misisnik/ExternalInterface/sw/display/window.py

"""
display window
====================
.. moduleauthor:: Michal Sladecek <misisnik@gmail.com>
.. autoclass:: GUI
.. autofunction:: lib

"""
from PIL import Image
from PIL import ImageDraw
from PIL import ImageFont

import os

system_fonts = {'Arial' : 'arial.ttf', 'Big' : 'big.ttf', 'Tiny' : 'tiny.ttf', 'Japan1': 'jpn/7pxkbus.TTF', 'Japan2': 'jpn/enksh__.ttf', 'Japan3': 'jpn/musekinin-katakana.TTF'}
disp_width = 192
disp_height = 64

class GUI(object):
	"""
		There is class for support graphic part of display
	"""
	def __init__(self, rotation = 0):
		"""
			inicialization of gui class
		"""
		#visualisation data - default is blank screen -> every px is off
		self.rotation = rotation #degree of window rotation
		self.reset()
		self.changed = False
		self.display_width = disp_width
		self.display_height = disp_height

	def reset(self):
		"""
			Reset all screen 
		"""
		self.data = [0x00] * 1536
		#create new image object
		if self.rotation == 90:
			self.display_width = disp_height
			self.display_height = disp_width
		else:
			self.display_width = disp_width
			self.display_height = disp_height
		self.image = Image.new('1', (self.display_width, self.display_height))
		self.draw = ImageDraw.Draw(self.image)

	def getBitmap(self, vertical = True):
		"""
			Get finish picture which has to show on display - generating bitmap array
		"""

		d = [""]*1536
		if vertical:
			#for ist3020
			self.finall_image = self.image.rotate(self.rotation)
			dat = self.finall_image.load()
			page = 0
			for i in range(0, self.display_height):
				if i%8 == 0 and i != 0:
					page += 1
				for c in range(0, self.display_width):
					if dat[(c,i)] == 255:
						dat[(c,i)] = 1
					d[(page * self.display_width) + c] += str(dat[(c,i)])
		else:
			#matrix orbital
			dat = self.image.load()
			data = ""
			c = 1
			for r in range(64):
				for l in range(192):
					data += str(dat[(l, r)])
			for i in range(1536):
				d[i] = data[i*8:(i*8)+8]
			#for matrix orbithal
		self.data = [int(i,2) for i in d]

	def addMultilineText(self, text, size = 10, x = 0, y = 0, align = "left", f = 'Arial', spacing = 1, fill = 1):
		"""
			Add multiline text to picture 
				text - data of text
				size - px size of letter
				x	 - x position
				y	 - y position

			return total lines, lines to print, array of text
		"""
		if align not in ['left', 'center', 'right']:
			align = 'left'
		#get width of text
		text_width, text_height = self.getMultilineTextSize(text, size, f)
		lines = 1
		lines_to_print = 1
		new_text = []
		#multiline text - parse to more line
		if text_width > self.display_width or text_height > self.display_height:
			longest = 0
			lines = 0
			new_text = [""]
			for i in text:
				wn, hn = self.getMultilineTextSize(new_text[-1], size, f)
				if wn > self.display_width:
					#check if we're not in the midle of world
					last = new_text[-1]
					for count, l in enumerate(last[::-1]):
						if l == " ":
							break;
					if count > 0 and count < 10:
						del new_text[-1]
						new_text.append(last[0:len(last) - count])
						new_text.append(last[len(last) - count:])
					else:
						new_text.append("")

				if i == "\n":
					new_text.append("")
				else:
					new_text[-1] += i
			lines = len(new_text)
			#calculate number of writing lines

			wt, ht = self.getTextSize(text, size, f)
			lines_to_print = int(self.display_height/(ht + spacing))
			text = "\n".join(new_text[0:lines_to_print])
			text_width, text_height = self.getMultilineTextSize(text, size, f)
		#align setting if is just 1line text -> smaller than self.display_width
		if text_width < self.display_width and x == 0:
			if align == "center":
				x = (self.display_width - text_width)/2
			elif align == "right":
				x = self.display_width - text_width

		#define font
		ph = os.path.dirname(os.path.realpath(__file__))
		font = ImageFont.truetype('{0}/fonts/{1}'.format(ph, system_fonts[f]), size)
		self.changed = True
		self.draw.multiline_text((x,y), str(text), font=font, fill = fill, align = align, spacing = spacing)
		return (lines, lines_to_print, new_text)

	def addText(self, text, size, x = 0, y = 0, align = "left", f = 'Arial', fill = 1, align_parameter = 0):
		"""
			Add text
		"""
		#get width of text
		text_width, text_height = self.getTextSize(text, size, f)

		#align setting if is just 1line text -> smaller than self.display_width
		if text_width < self.display_width and x == 0:
			if align == "center":
				x = ((self.display_width - text_width)/2) + align_parameter
			elif align == "right":
				x = self.display_width - text_width + align_parameter

		ph = os.path.dirname(os.path.realpath(__file__))
		font = ImageFont.truetype('{0}/fonts/{1}'.format(ph, system_fonts[f]), size)
		self.changed = True
		self.draw.text((x,y), str(text), font=font, fill = fill)	#can be draw.text....
		return text_width, text_height

	def addArc(self, start, end, first = [0, 0], second = [0, 0], fill = 1):
		"""
			Add an arc (a portion of a circle outline) between the start and end angles, inside the given bounding box.
				start	-	starting angle in degrees
				end		-	ending angle in degrees
		"""
		self.changed = True
		self.draw.arc([first[0], first[1], second[0], second[1]], start, end, fill = fill)

	def addChord(self, start, end, first = [0, 0], second = [0, 0], fill = 1):
		"""
			Same as addArc but the end points with a straight line
		"""
		self.changed = True
		self.draw.chord([first[0], first[1], second[0], second[1]], start, end, fill = fill)

	def addEllipse(self, first = [0, 0], second = [0, 0], fill = True):
		"""
			Add ellipse
				fill == True then elipse is filled (1)
				fill == False then elipse is not filled (0)
				first 	 == array of x0 and y0
				second	 == array of x1 and y1
		"""
		self.changed = True
		self.draw.ellipse([first[0], first[1], second[0], second[1]], fill = fill, outline = not fill)

	def addLine(self, first = [0, 0], second = [0, 0], width = 0, fill = 1):
		"""
			Add line
				first 	 == array of x0 and y0
				second	 == array of x1 and y1
				width = width of line
		"""
		self.changed = True
		self.draw.line([first[0], first[1], second[0], second[1]], fill = fill, width = width)

	def addPoint(self, position = [(0,0)], fill = 1):
		"""
			Add points
				position array of (x,y) position of points
		"""
		self.changed = True
		self.draw.point(position, fill = fill)

	def addPolygon(self, position = [(0,0)], fill = True):
		"""
			Add polygon 
			The polygon outline consists of straight lines between the given coordinates, plus a straight line between the last and the first coordinate.
		"""
		self.changed = True
		self.draw.polygon(position, fill = fill, outline = not fill)

	def addRectangle(self, first = [0, 0], second = [0, 0], fill = True):
		"""
			Add rectangle 
		"""
		self.changed = True
		self.draw.rectangle([first[0], first[1], second[0], second[1]], fill = fill, outline = not fill)

	#finally get some information
	def getMultilineTextSize(self, text, size, f = 'Arial'):
		"""
			get text size
		"""
		ph = os.path.dirname(os.path.realpath(__file__))
		font = ImageFont.truetype('{0}/fonts/{1}'.format(ph, system_fonts[f]), size)
		return self.draw.multiline_textsize(str(text), font)

	def getTextSize(self, text, size, f = 'Arial'):
		"""
			get text size
		"""
		ph = os.path.dirname(os.path.realpath(__file__))
		font = ImageFont.truetype('{0}/fonts/{1}'.format(ph, system_fonts[f]), size)
		return self.draw.textsize(str(text), font)

	def clear(self, position = [[0,0], [192, 64]], fill = False):
		"""
			clear part of window wchich is defined by position
				position - [[x0, y0], [x1, y1]]
			basicly add white place - rectangle
		"""
		self.draw.rectangle([position[0][0], position[0][1], position[1][0], position[1][1]], fill = fill, outline = fill)

	def addImage(self, img, position = [0, 0], reverse = False):
		"""
			add image from file
				img - file to load
		"""
		self.changed = True
		img = Image.open(img).convert('1')

		width, height = img.size
		if width > self.display_width or height > self.display_height:
			#have to resize
			img = img.resize((self.display_width, self.display_height), Image.NEAREST)

		if not reverse:
			pixdata = img.load()
			for y in range(img.size[1]):
				for x in range(img.size[0]):
					if pixdata[x, y] == 255:
						pixdata[x, y] = 0
					else:
						pixdata[x, y] = 1

		self.image.paste(img, (position[0], position[1]))
